limitium/limitium-datcyl-manuform/gallery/20210916.jpg

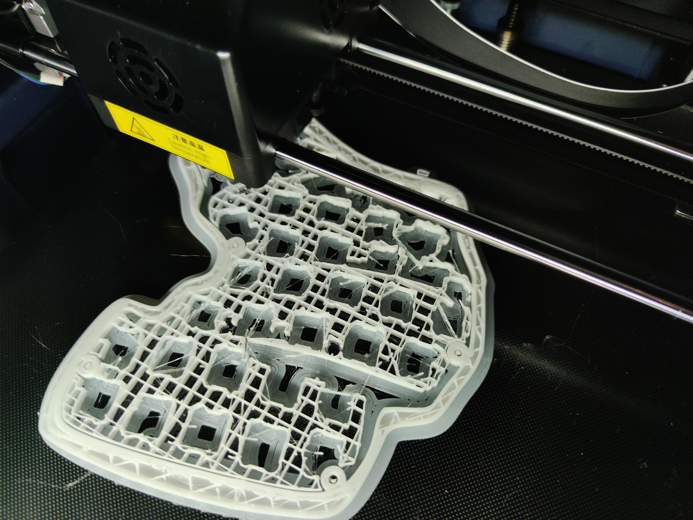
gallery/20210916.jpg
