limitium/limitium-datcyl-manuform/gallery/20210924.jpg

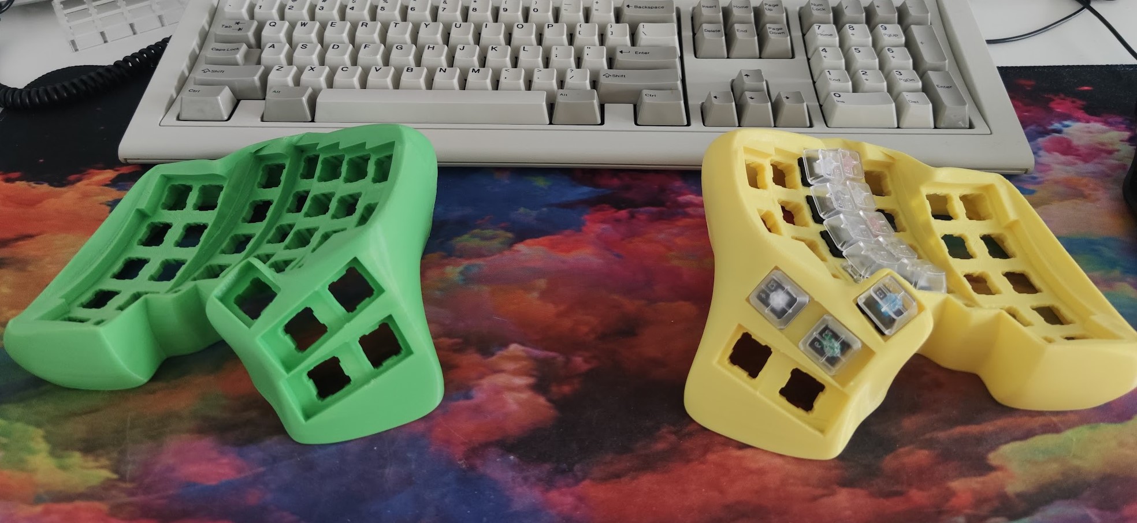
gallery/20210924.jpg
