limitium/limitium-datcyl-manuform/gallery/20210930.jpg

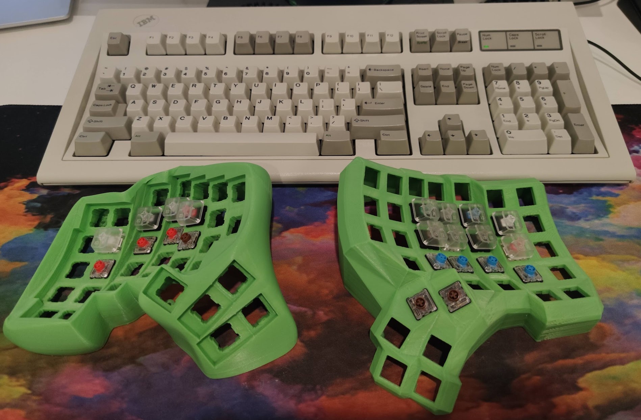
gallery/20210930.jpg
