limitium/limitium-datcyl-manuform/gallery/20211008_2.jpg

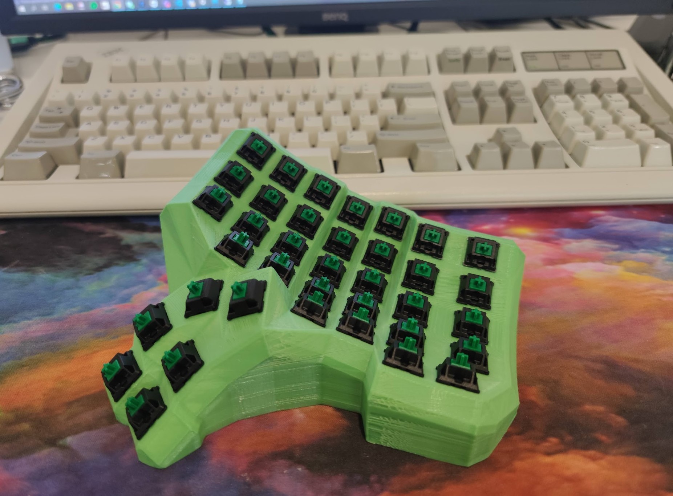
gallery/20211008_2.jpg
