limitium/limitium-datcyl-manuform/gallery/20211008_3.jpg

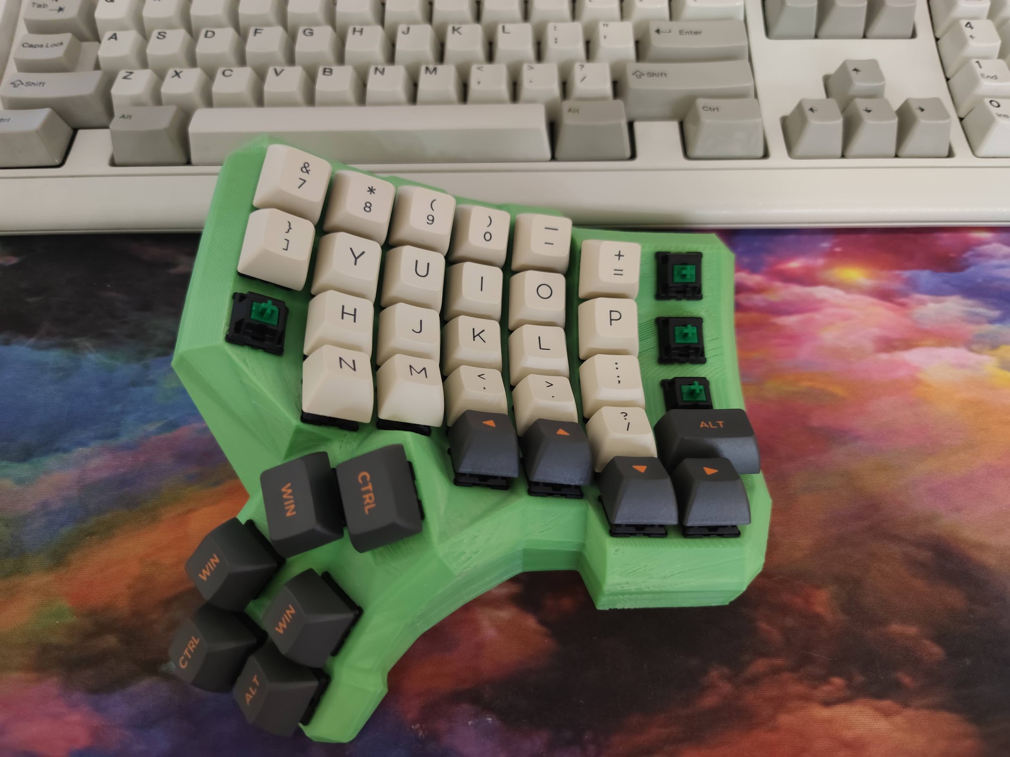
gallery/20211008_3.jpg
