limitium/limitium-datcyl-manuform/gallery/20211009.jpg

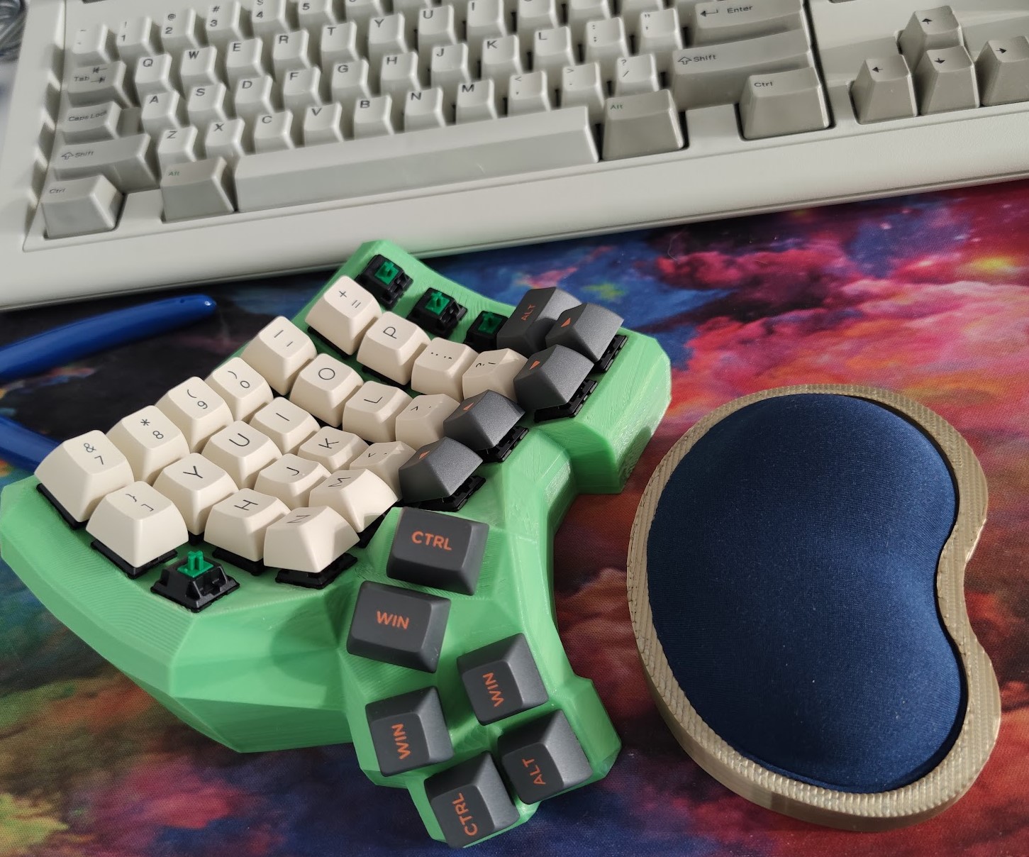
gallery/20211009.jpg
