limitium/limitium-datcyl-manuform/gallery/20211012.jpg

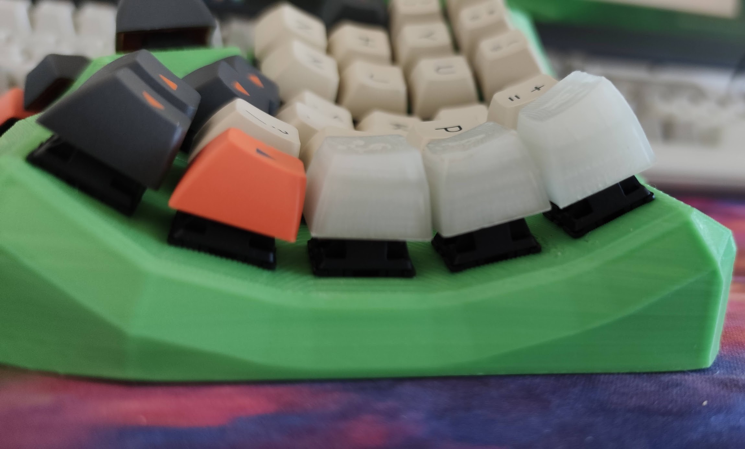
gallery/20211012.jpg
