limitium/limitium-datcyl-manuform/gallery/20211014_2.jpg

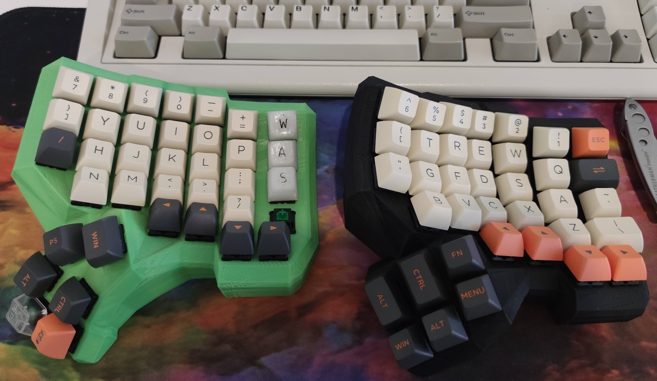
gallery/20211014_2.jpg
