limitium/limitium-datcyl-manuform/gallery/20211020.jpg

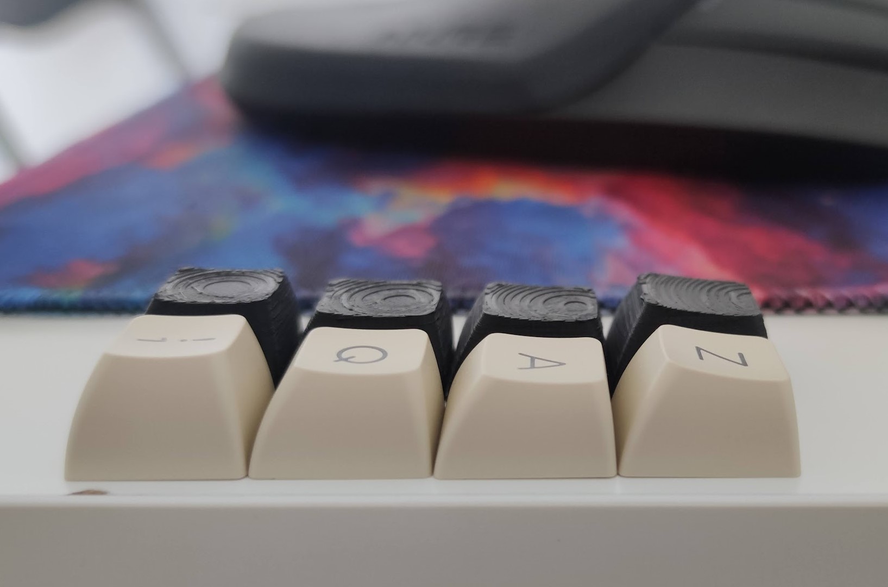
gallery/20211020.jpg
