limitium/limitium-datcyl-manuform/gallery/20211020_2.jpg

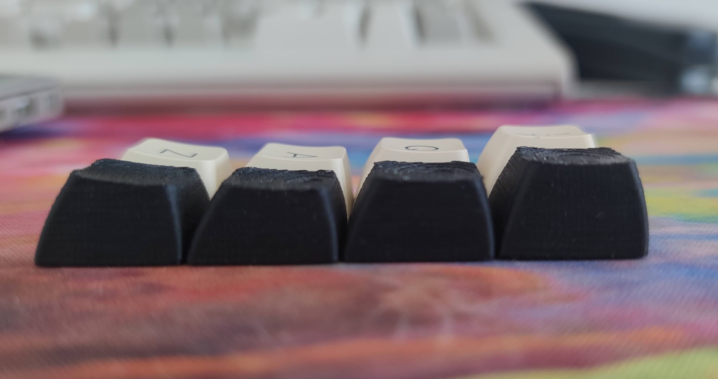
gallery/20211020_2.jpg
