limitium/limitium-datcyl-manuform/gallery/20211020_3.jpg

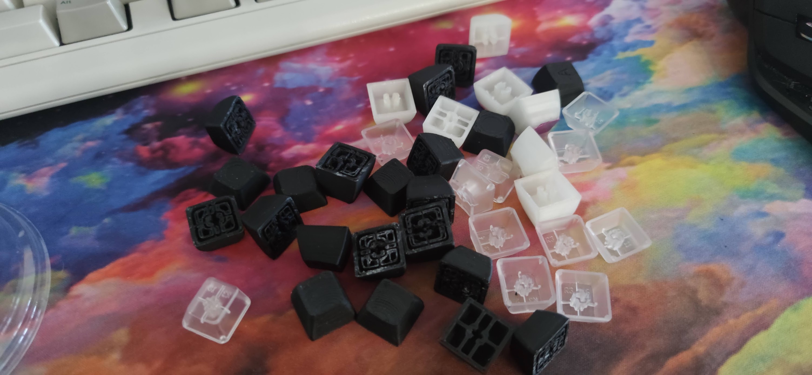
gallery/20211020_3.jpg
