limitium/limitium-datcyl-manuform/gallery/20211203.jpg

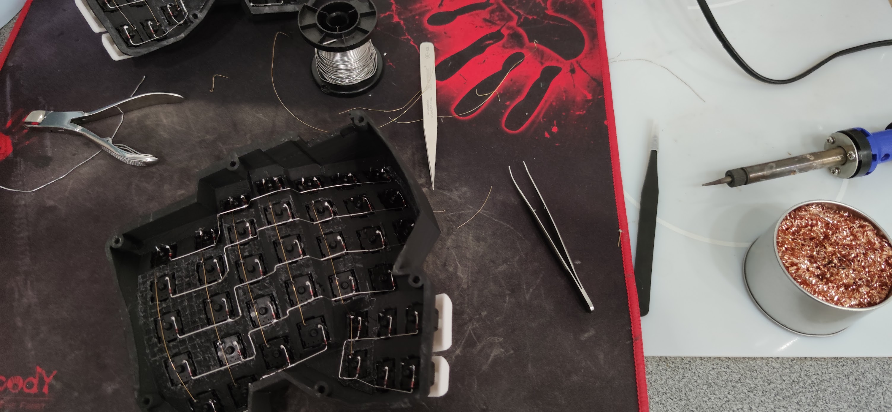
gallery/20211203.jpg
