limitium/limitium-datcyl-manuform/gallery/20211203_2.jpg

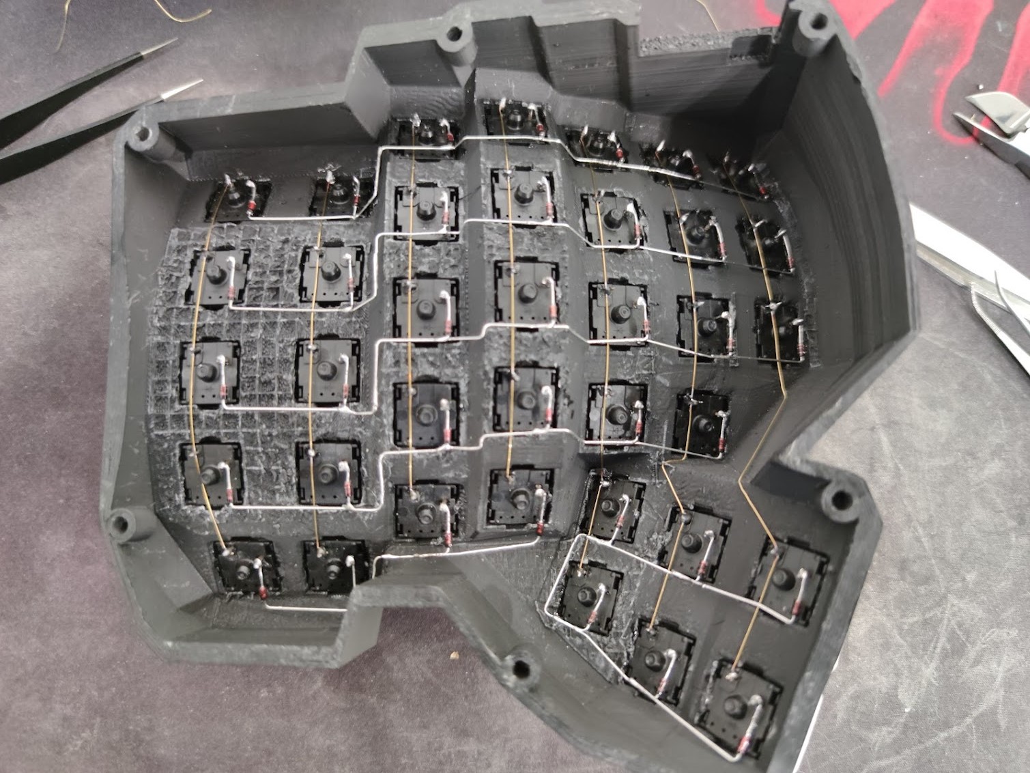
gallery/20211203_2.jpg
