limitium/limitium-datcyl-manuform/gallery/20211206_4.jpg

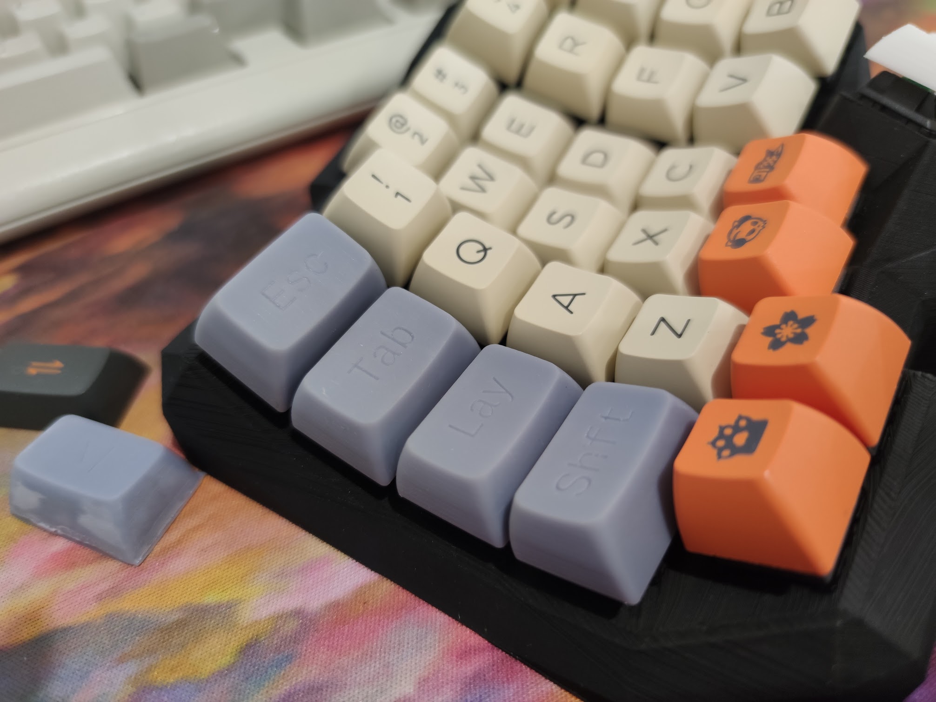
gallery/20211206_4.jpg
