limitium/limitium-datcyl-manuform/gallery/20211207.jpg

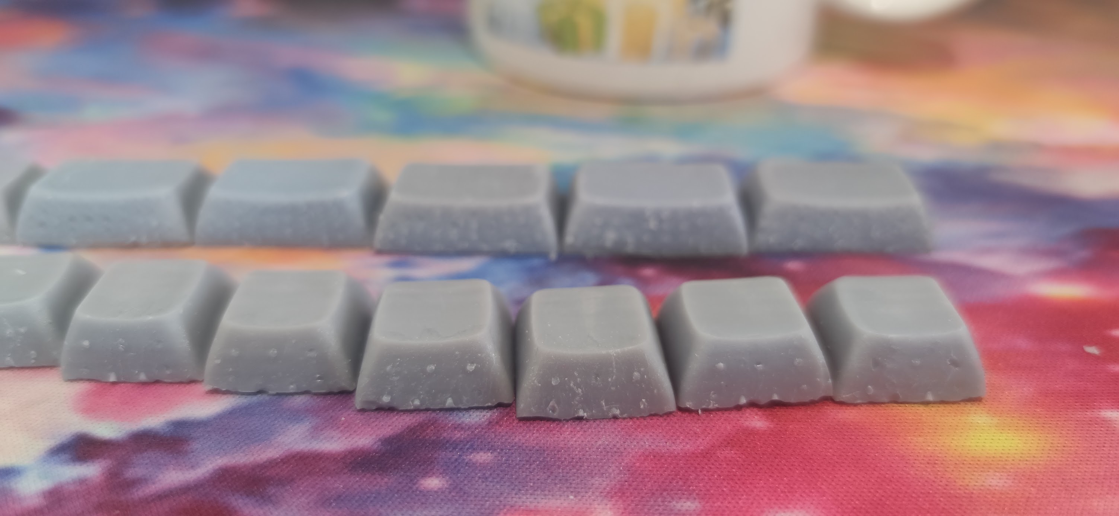
gallery/20211207.jpg
