limitium/limitium-datcyl-manuform/gallery/20220123_2.jpg

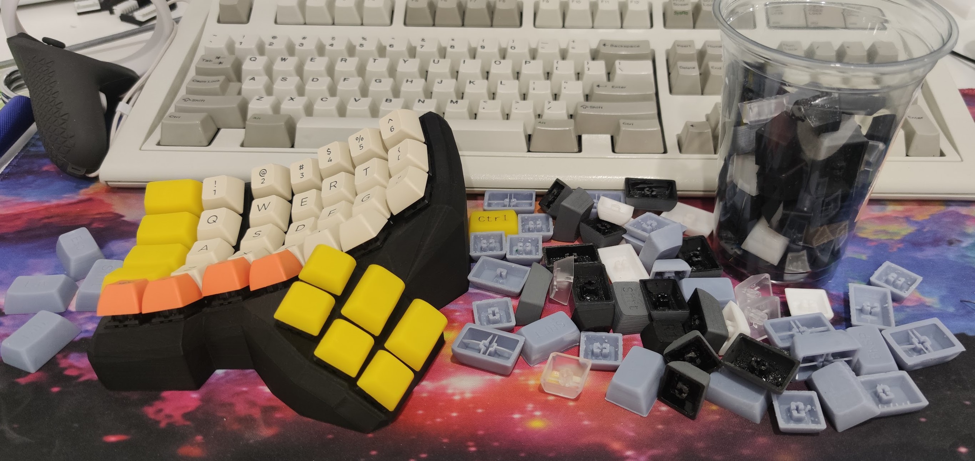
gallery/20220123_2.jpg
