limitium/limitium-datcyl-manuform/gallery/20220123_3.jpg

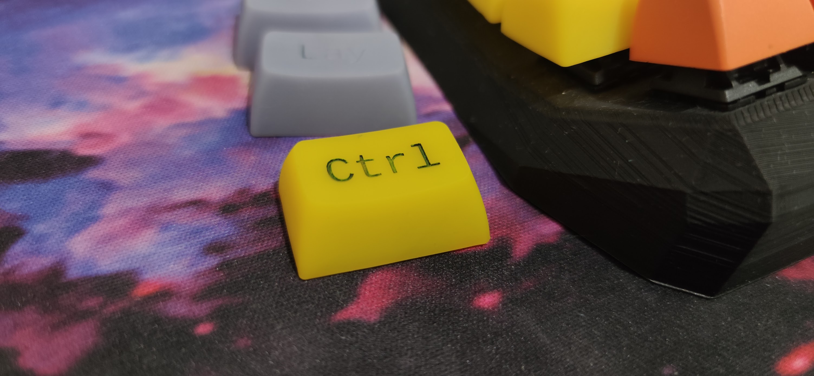
gallery/20220123_3.jpg
