limitium/limitium-datcyl-manuform/gallery/20220123_4.jpg

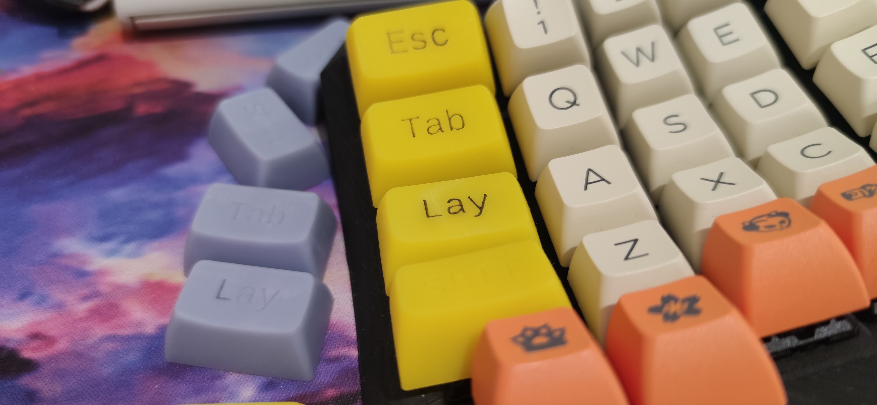
gallery/20220123_4.jpg
