limitium/limitium-datcyl-manuform/gallery/20220123_5.jpg

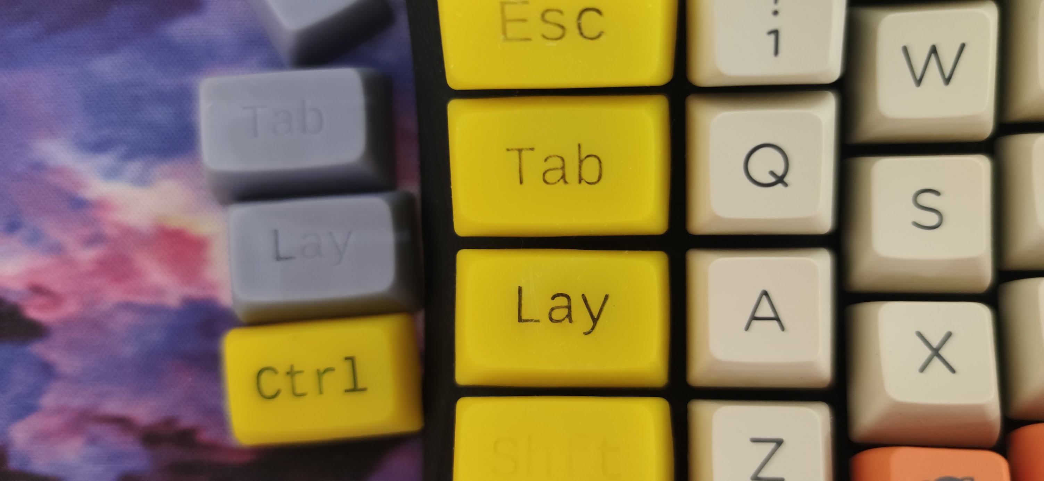
gallery/20220123_5.jpg
