limitium/limitium-datcyl-manuform/gallery/20220124.jpg

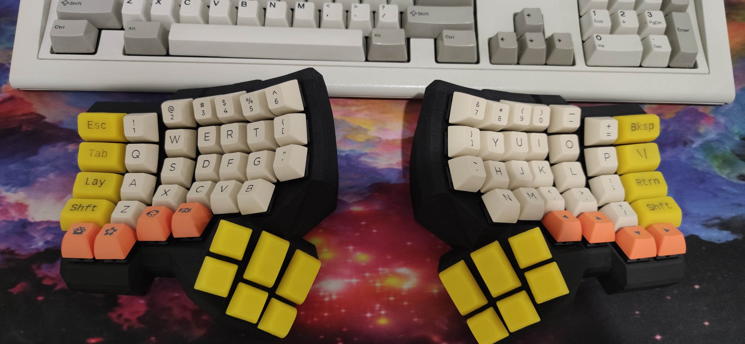
gallery/20220124.jpg
