limitium/limitium-datcyl-manuform/gallery/20220430.jpg

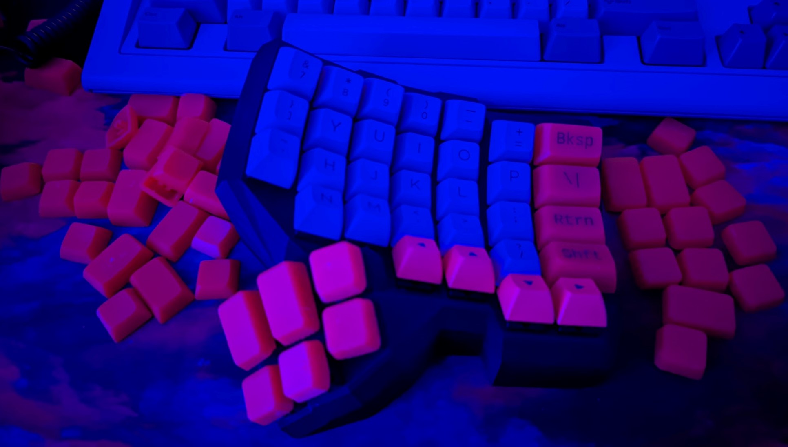
gallery/20220430.jpg
