limitium/limitium-datcyl-manuform/gallery/20220512_2.jpg

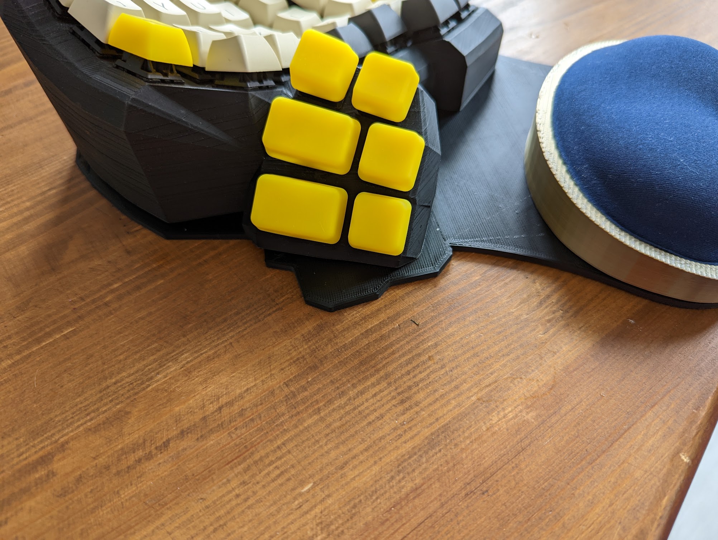
gallery/20220512_2.jpg
