limitium/limitium-datcyl-manuform/gallery/20220515.jpg

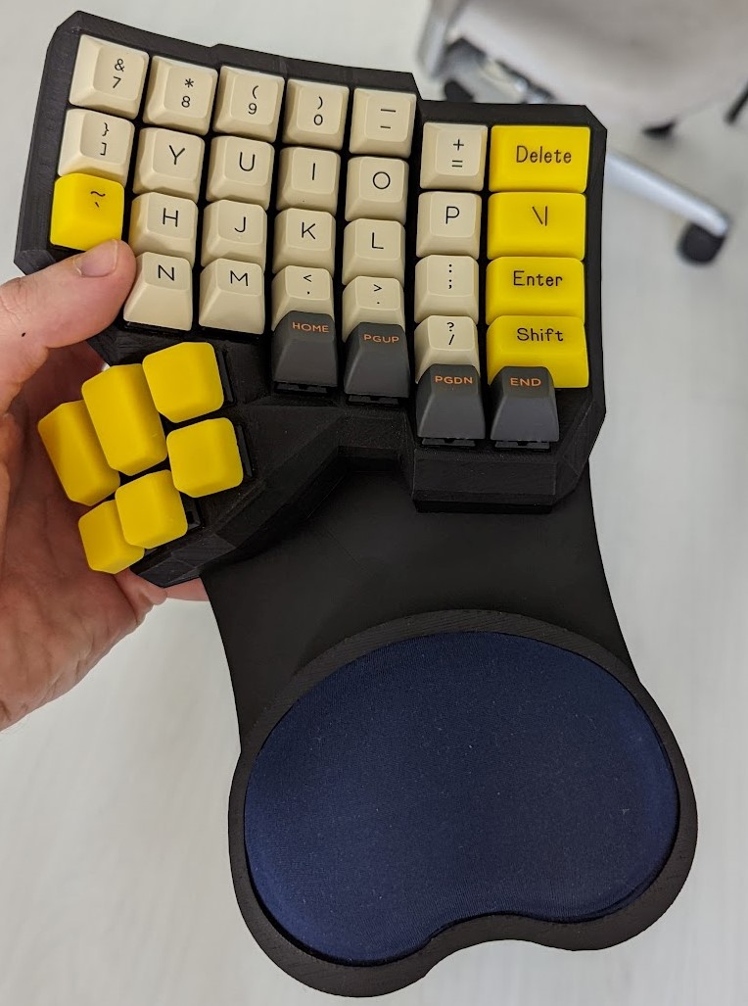
gallery/20220515.jpg
