limitium/limitium-datcyl-manuform/gallery/20220515_2.jpg

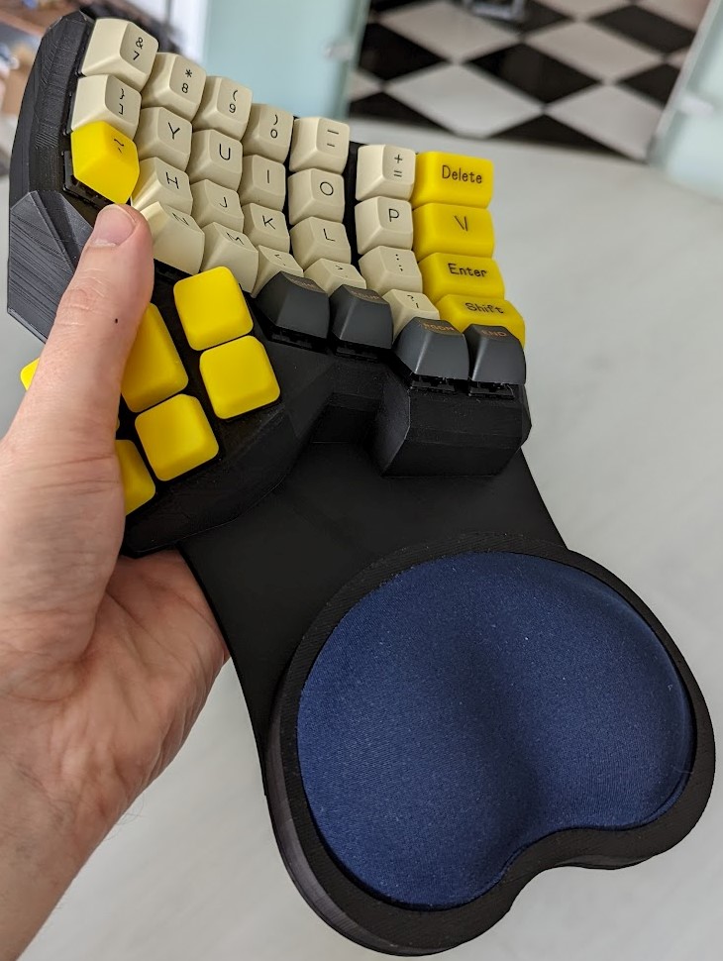
gallery/20220515_2.jpg
