limitium/limitium-datcyl-manuform/gallery/20220822_2.jpg

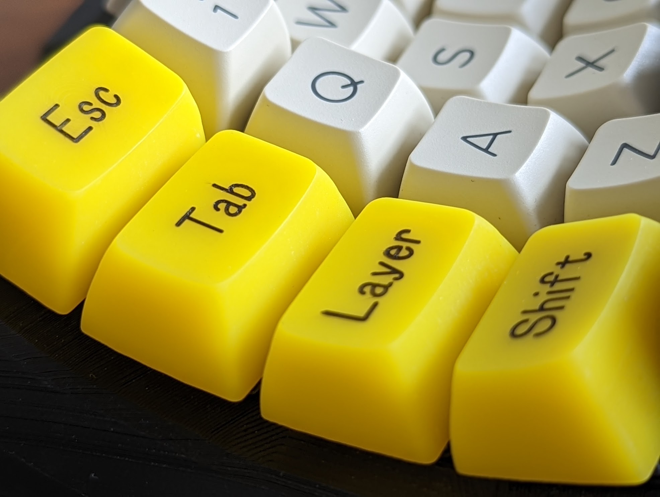
gallery/20220822_2.jpg
