limitium/limitium-datcyl-manuform/gallery/20220822_3.jpg

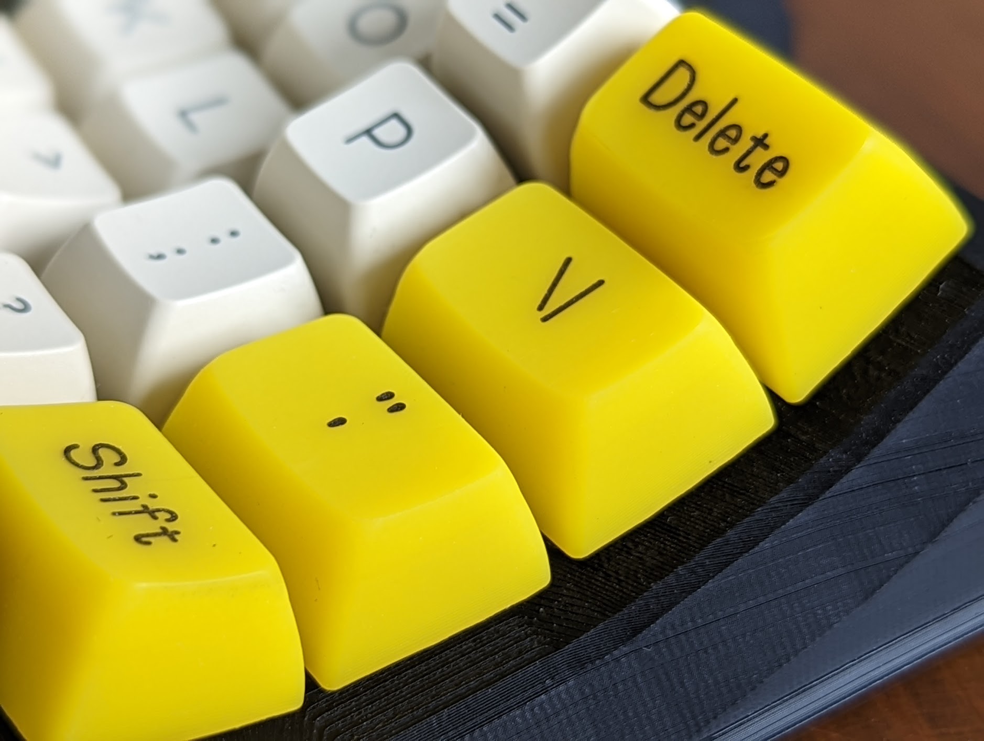
gallery/20220822_3.jpg
