limitium/limitium-datcyl-manuform/gallery/20220822_6.jpg

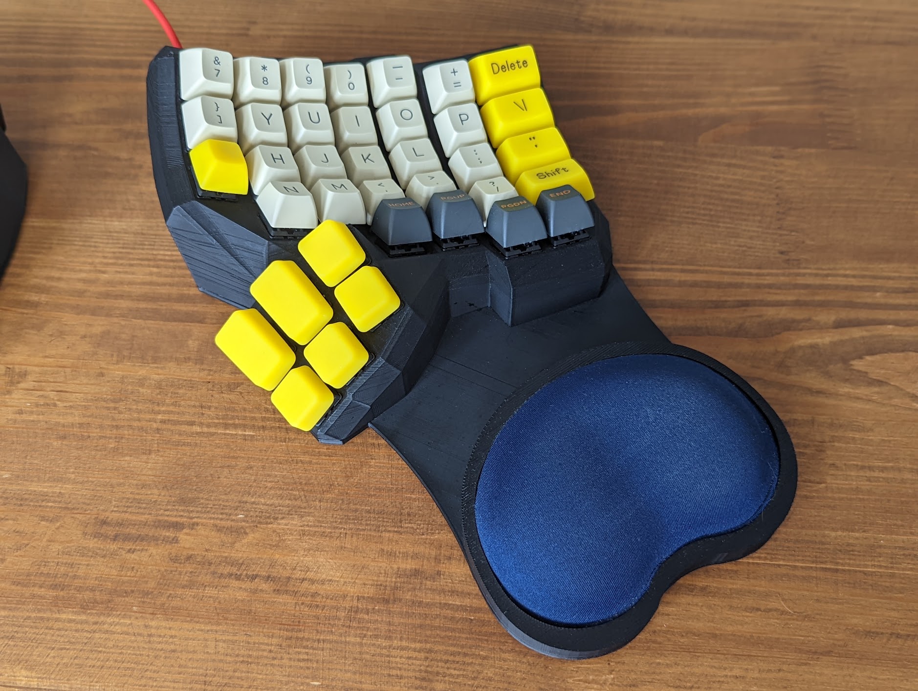
gallery/20220822_6.jpg
