limitium/limitium-datcyl-manuform/gallery/20220822_7.jpg

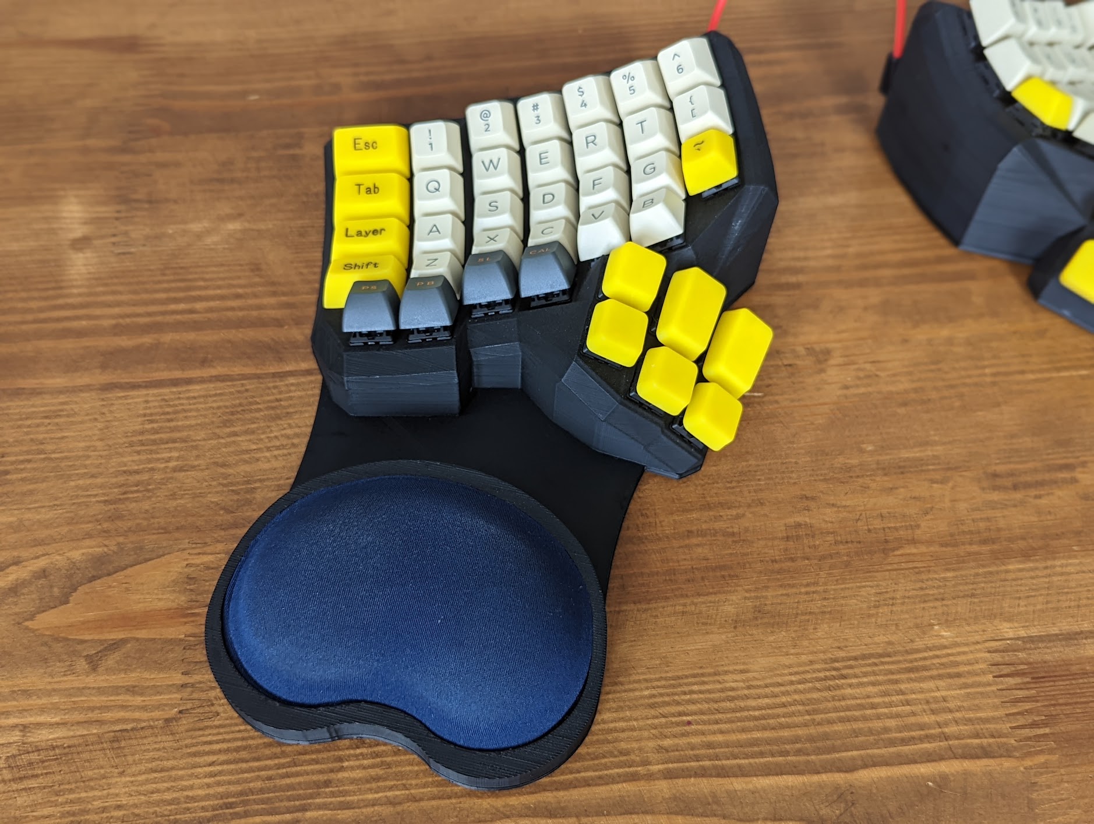
gallery/20220822_7.jpg
